roysmeding/induction-heater/sim/ltspice/work_coil_circuit.asc

C_Ctank: cap; 1.65µ; Rser=0 Lser=0 Cpar=0
L_Ctank: ind; 5n; Rser=0
L_Loutput: ind2; 1.5µ; Rser=0
L_Tcouple_A: ind2; 1m; Rser=0
L_Tcouple_B: ind2; 2.5µ; Rser=0
L_workpiece: ind2; 60n; Rser=0
R_Ctank: res; 1m
R_Loutput: res; 5m
R_Tcouple_A: res; 1m
R_Tcouple_B: res; 100µ
R_workpiece: res; {RL}
VA: voltage; PULSE(0 325 0 100n 100n {Ton} {T}); AC 162.5 0; Rser=0
VB: voltage; PULSE(0 325 {T/2} 100n 100n {Ton} {T}); AC 162.5 180; Rser=0
Named nets: 0, V_workpiece, V_VA, V_VB
Kwork L_Loutput L_workpiece 1
.tran 100m uic
Kcouple L_Tcouple_A L_Tcouple_B 1
.meas Pin AVG -V(V_VA)*I(VA) - V(V_VB)*I(VB)
.meas Pout AVG V(V_workpiece)*I(R_workpiece)
.meas Pworkcoil AVG V(N004,N007)*I(R_Loutput)
.meas Ptankcaps AVG V(N002,N003)*I(R_Ctank)
.meas Pcouple AVG V(N001,N006)*I(R_Tcouple_B)
.meas Ploss PARAM Pworkcoil+Ptankcaps+Pcouple
.meas eff PARAM Pout/Pin
.param RL 0.05
.param D = 1
.param T 10u
.param Ton = (T/2)*D
